miharix/miharix-wifi-rc/Arduino/simple/Landsailer2servoSlo/Screenshot_nexus4.png

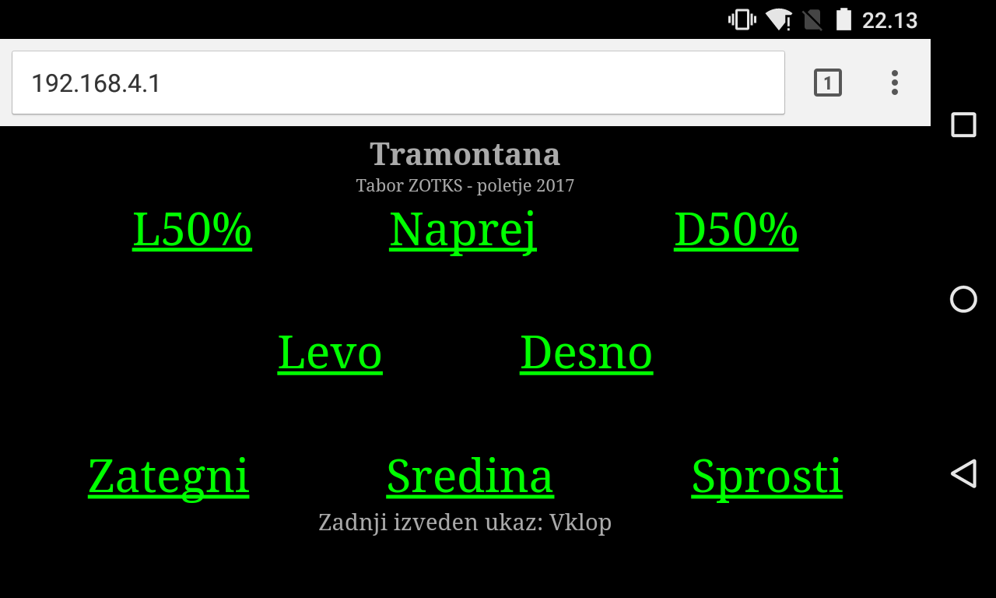
Arduino/simple/Landsailer2servoSlo/Screenshot_nexus4.png
