miharix/miharix-wifi-rc/Arduino/socket/socket-2servo-nice/Screenshot_nexus4.png

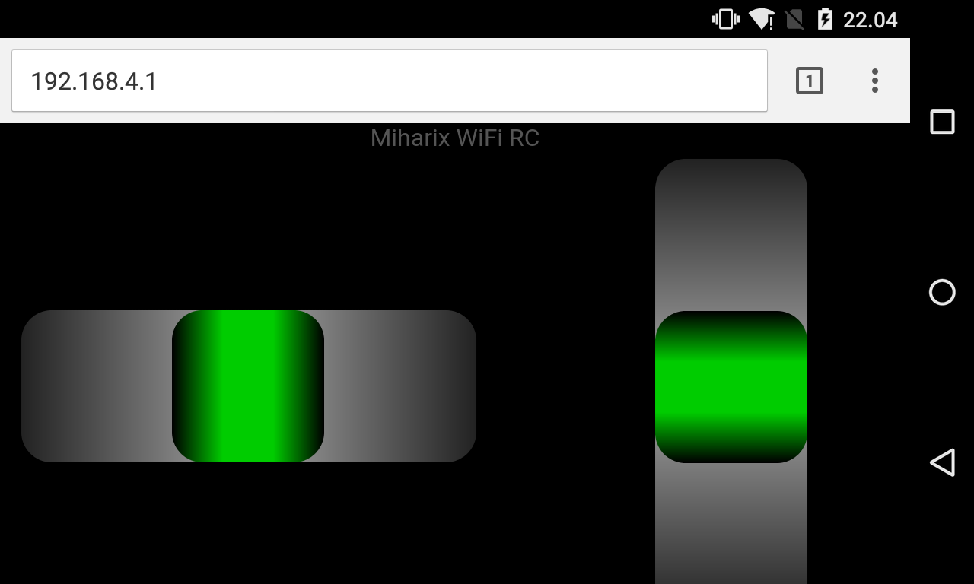
Arduino/socket/socket-2servo-nice/Screenshot_nexus4.png
