miharix/miharix-wifi-rc/Arduino/socket/socket-2servo-slo/Screenshot_nexus4.png

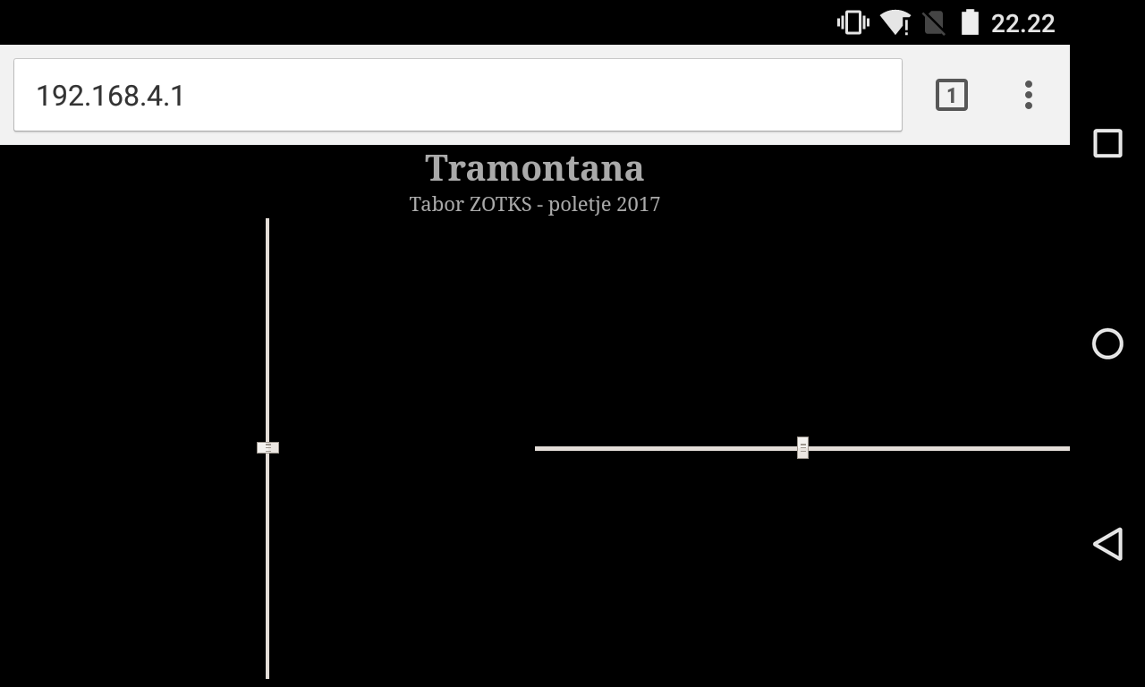
Arduino/socket/socket-2servo-slo/Screenshot_nexus4.png
