miharix/miharix-wifi-rc/Arduino/socket/socket-6servo-advance/Screenshots/Screenshot_nexus4_CONTROL8.png

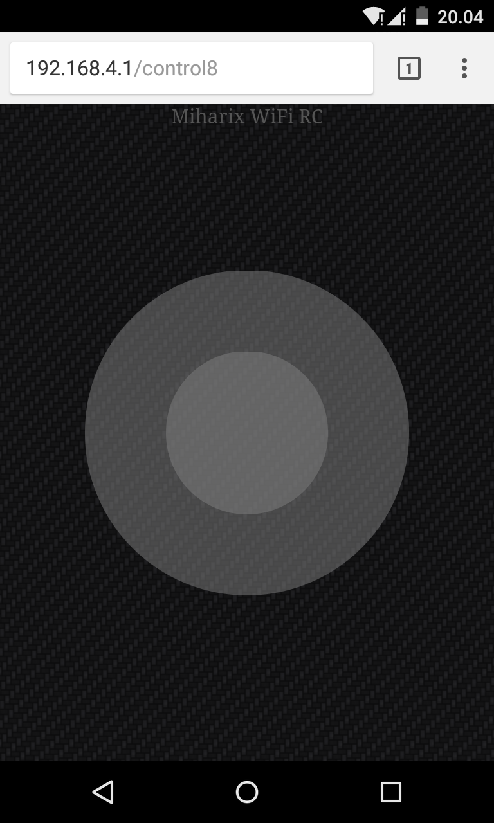
Arduino/socket/socket-6servo-advance/Screenshots/Screenshot_nexus4_CONTROL8.png
