miharix/miharix-wifi-rc/Arduino/socket/socket-6servo-advance/Screenshots/Screenshot_nexus4_CONTROL9.png

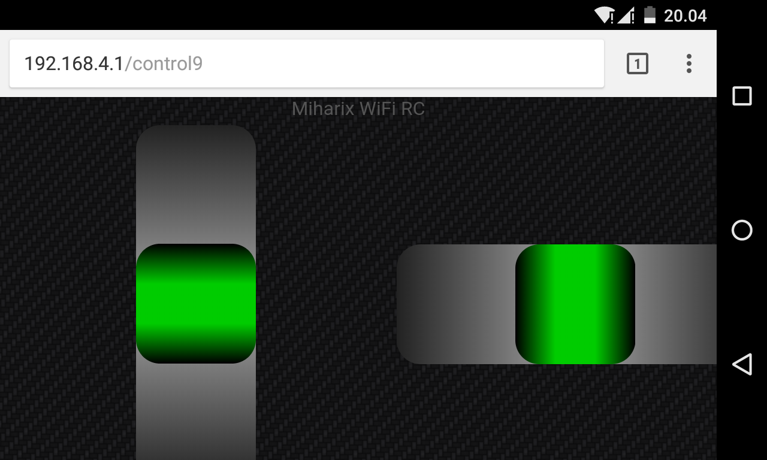
Arduino/socket/socket-6servo-advance/Screenshots/Screenshot_nexus4_CONTROL9.png
