miharix/miharix-wifi-rc/Documentation/ESP_servo_v3.png

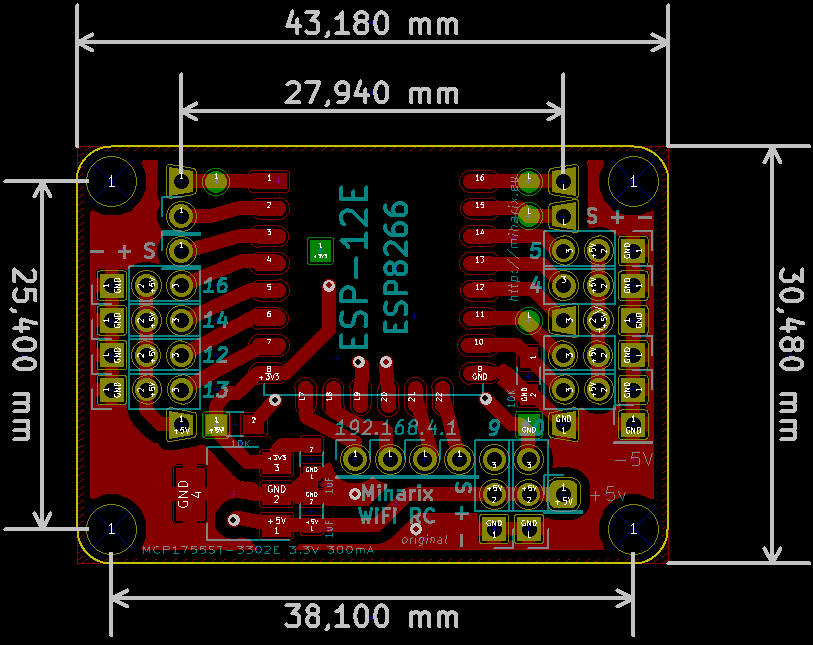
Documentation/ESP_servo_v3.png
