miharix/miharix-wifi-rc/Documentation/miharix_wiFi_mini_ENG.png

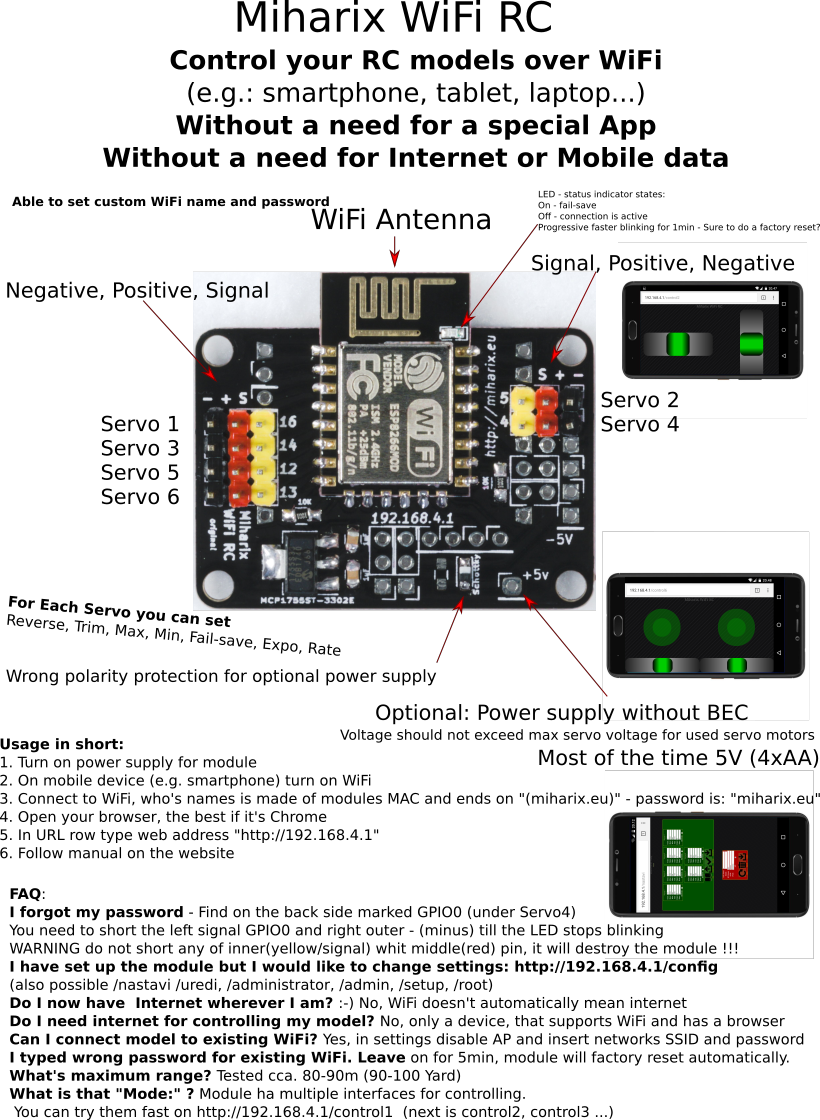
Documentation/miharix_wiFi_mini_ENG.png
