miharix/miharix-wifi-rc/model_examples/MobiRobi/MobiRobi.JPG

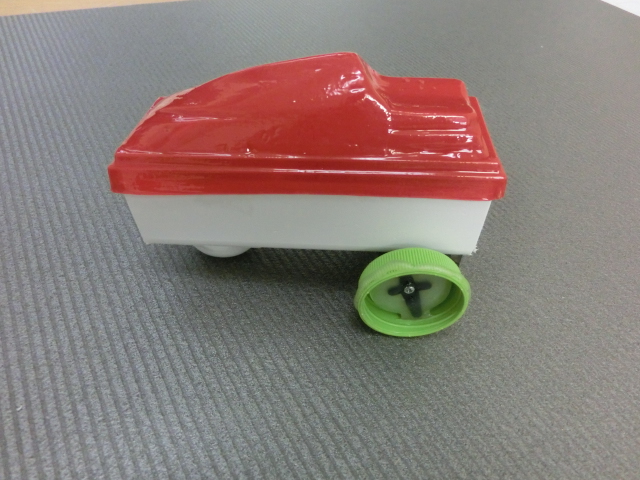
model_examples/MobiRobi/MobiRobi.JPG
