miharix/miharix-wifi-rc/model_examples/Sumpi/sumpi.jpg

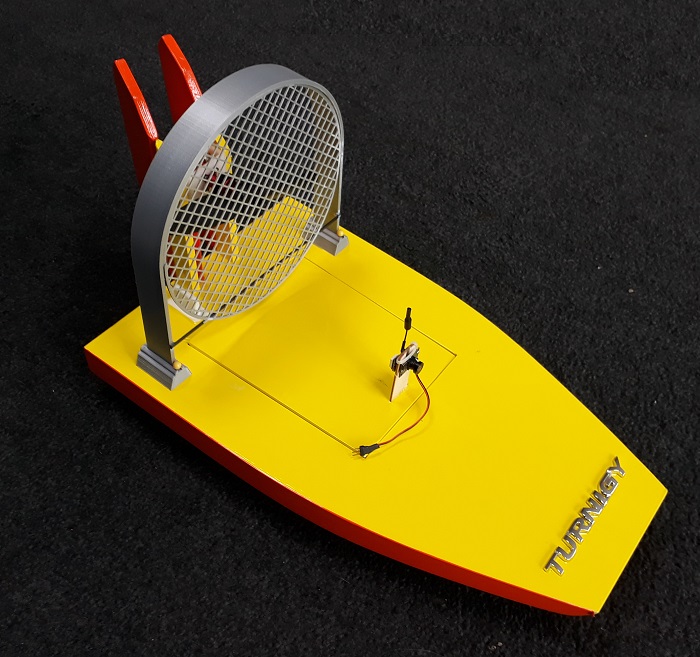
model_examples/Sumpi/sumpi.jpg
