miharix/miharix-wifi-rc/Render/V3/ESP_servo_v3_4.jpg

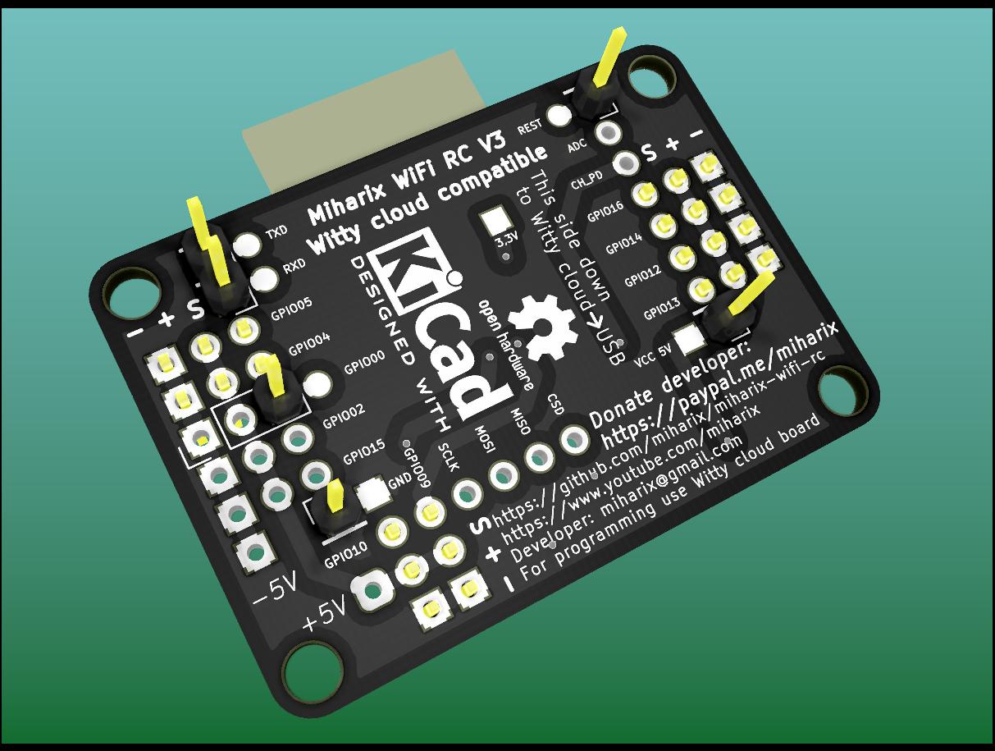
Render/V3/ESP_servo_v3_4.jpg
